ketszim97/TO_220_Buck/Renders/Photos/149419925_792506014680006_8886446949957860765_n.jpg

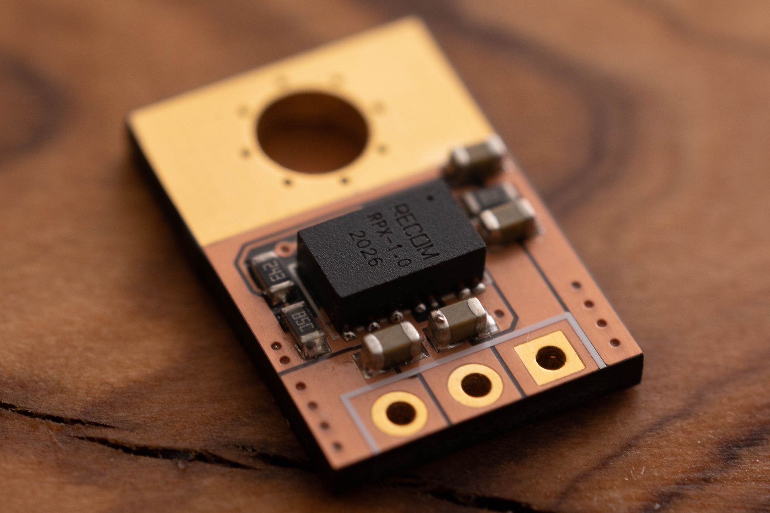
Renders/Photos/149419925_792506014680006_8886446949957860765_n.jpg
