ketszim97/TO_220_Buck/Renders/Photos/149459865_3474213502690533_5137175268388201964_n.jpg

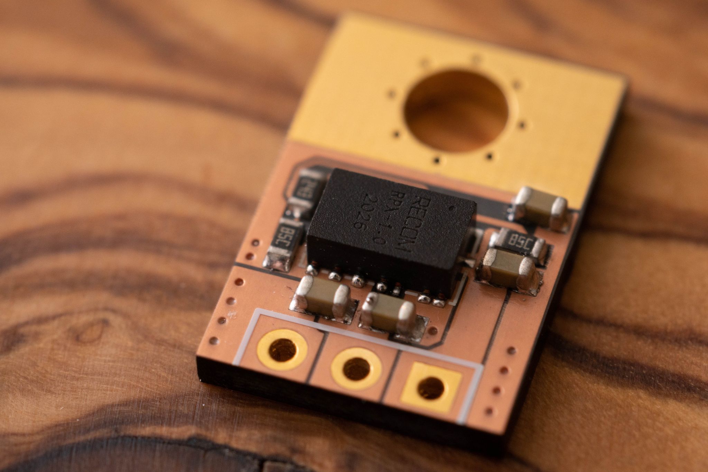
Renders/Photos/149459865_3474213502690533_5137175268388201964_n.jpg
