ketszim97/TO_220_Buck/Renders/Photos/149528836_711852932822343_8148399697909948898_n.jpg

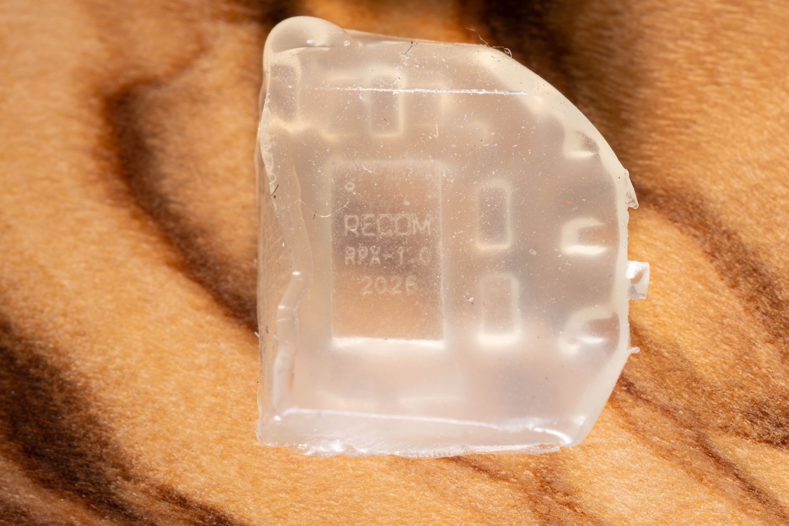
Renders/Photos/149528836_711852932822343_8148399697909948898_n.jpg
