ketszim97/TO_220_Buck/Renders/Photos/149537447_1244964915901211_925511400282466722_n.jpg

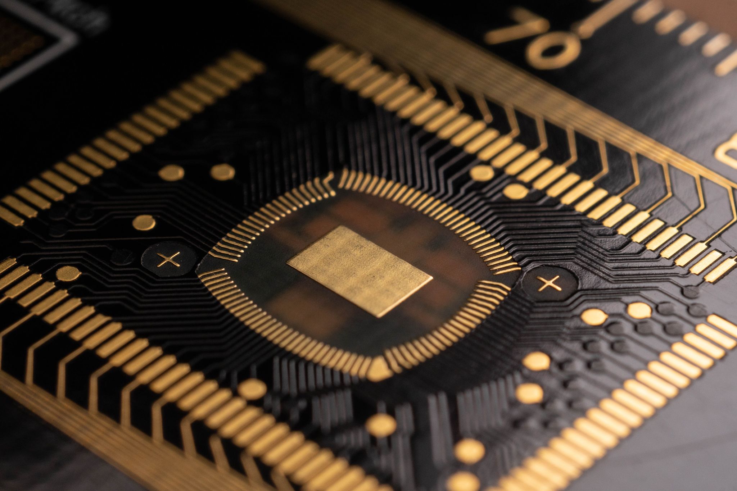
Renders/Photos/149537447_1244964915901211_925511400282466722_n.jpg
