ketszim97/TO_220_Buck/Renders/Photos/149566812_3517663008360148_2053222494374139507_n.jpg

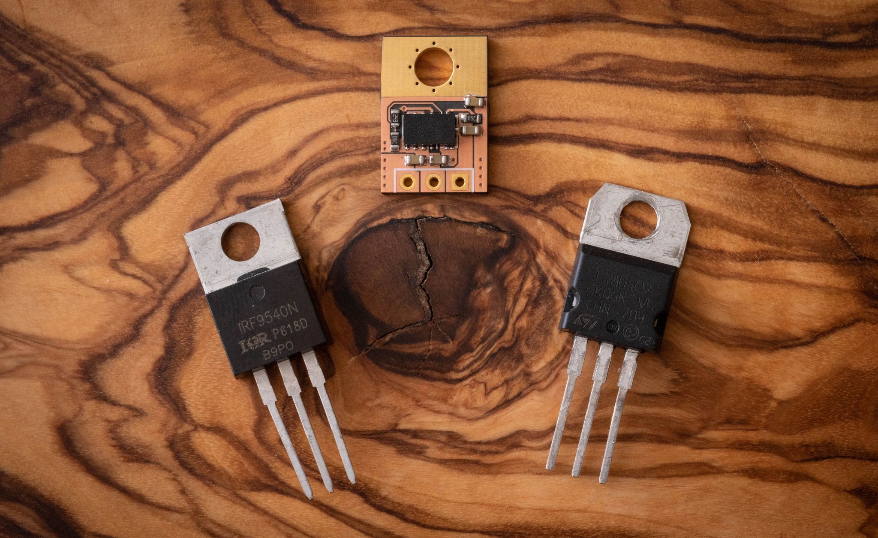
Renders/Photos/149566812_3517663008360148_2053222494374139507_n.jpg
