ketszim97/TO_220_Buck/Renders/Photos/149648833_326271058803372_157924160653448781_n.jpg

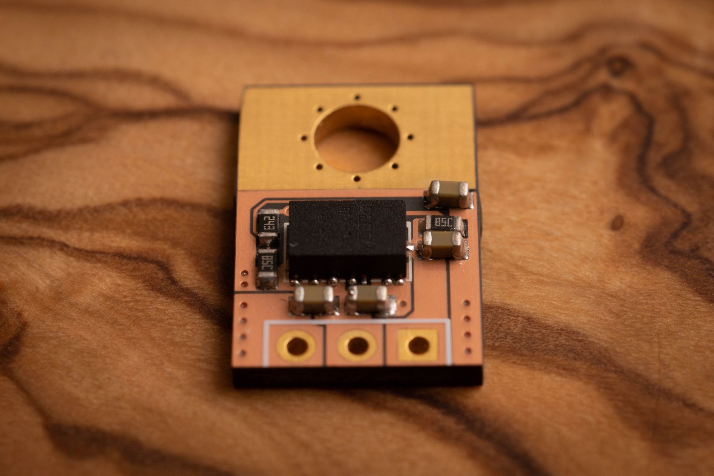
Renders/Photos/149648833_326271058803372_157924160653448781_n.jpg
