ketszim97/TO_220_Buck/Renders/Photos/149690482_248480446752142_3542841920429757807_n.jpg

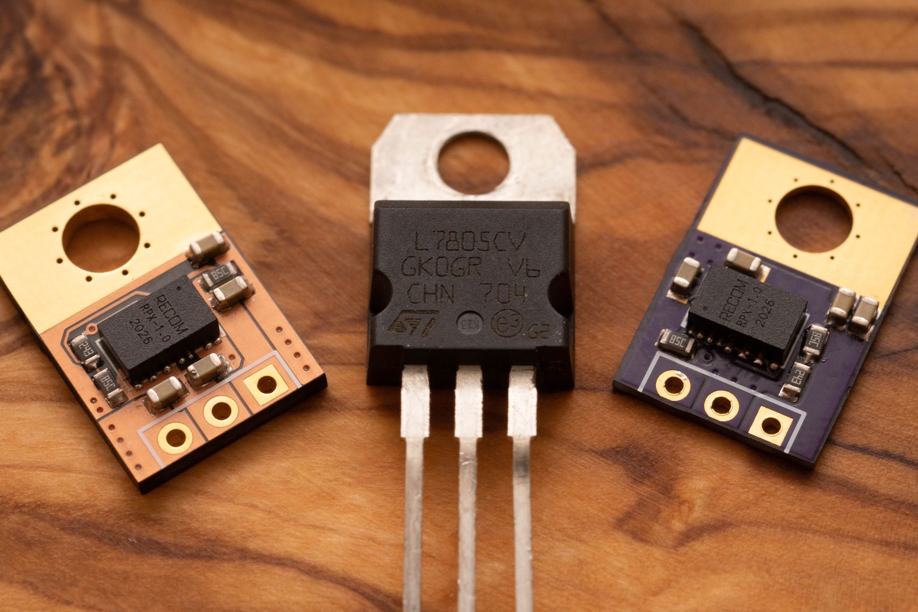
Renders/Photos/149690482_248480446752142_3542841920429757807_n.jpg
