ketszim97/TO_220_Buck/Renders/Photos/149705849_492895295441886_4602141825027261925_n.jpg

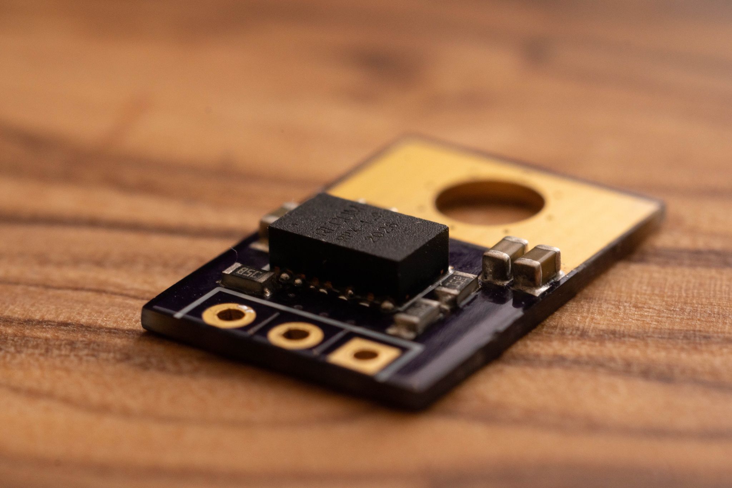
Renders/Photos/149705849_492895295441886_4602141825027261925_n.jpg
