ketszim97/TO_220_Buck/Renders/Photos/149872428_330163285035907_6420087823227812447_n.jpg

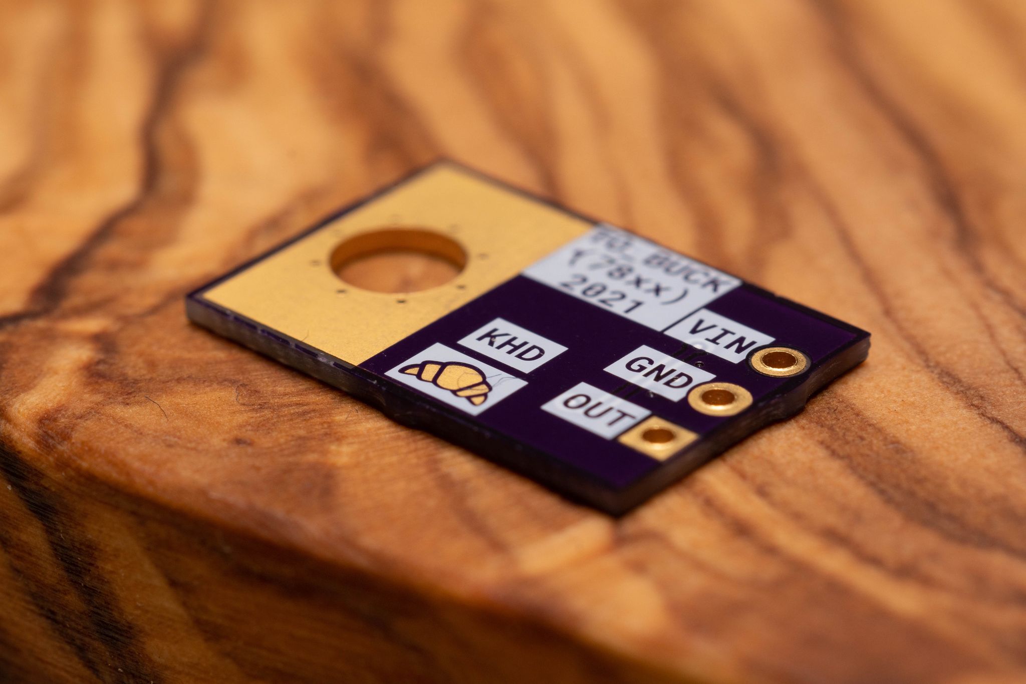
Renders/Photos/149872428_330163285035907_6420087823227812447_n.jpg
