ketszim97/TO_220_Buck/Renders/Photos/149902373_492424528822275_8873897516138256639_n.jpg

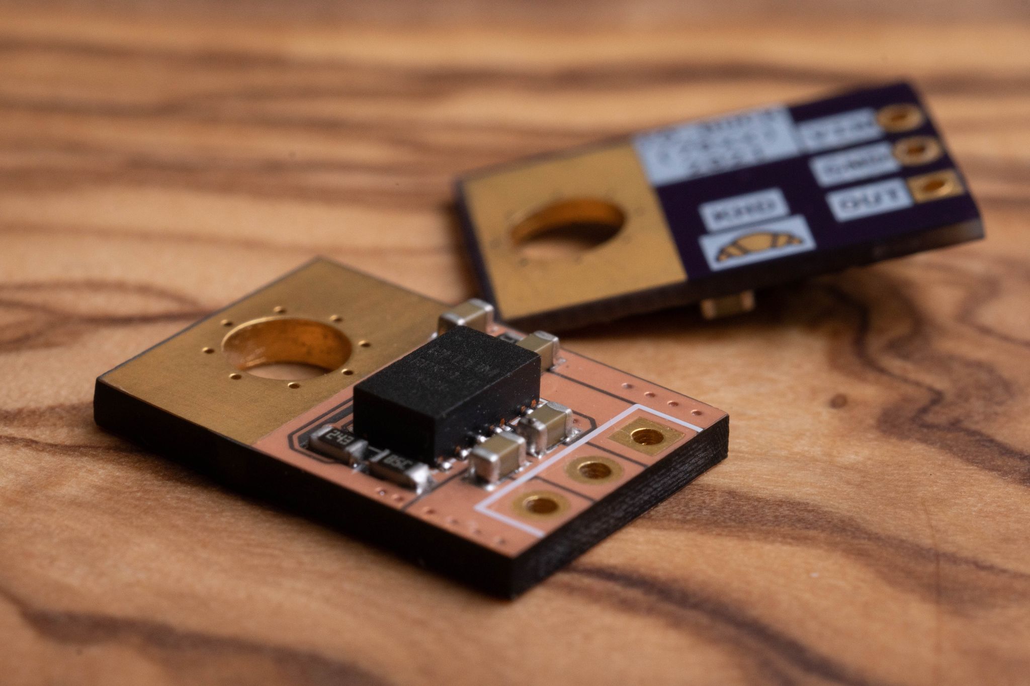
Renders/Photos/149902373_492424528822275_8873897516138256639_n.jpg
