ketszim97/TO_220_Buck/Renders/Photos/149912720_1985792348225276_4884634092275549586_n.jpg

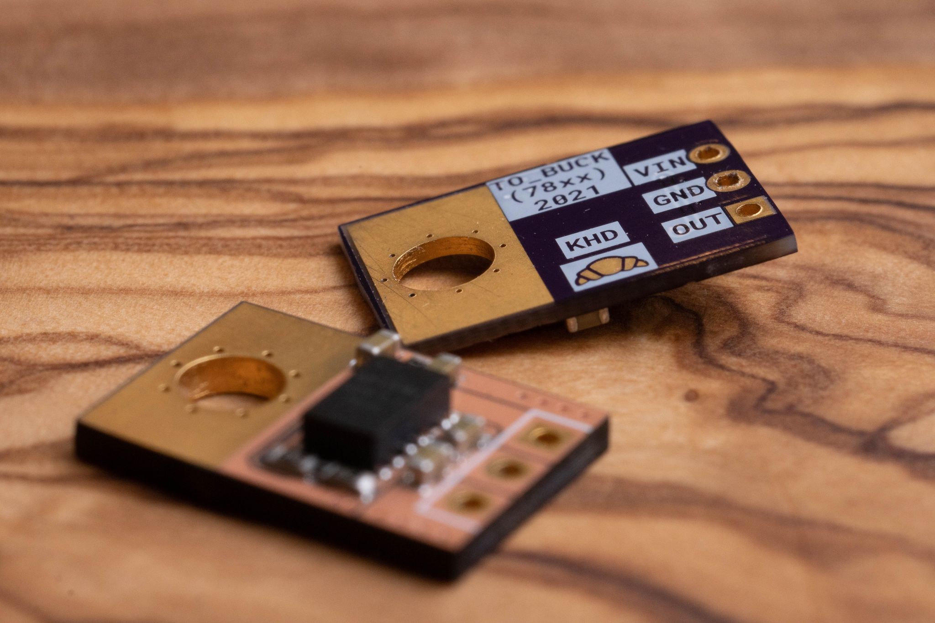
Renders/Photos/149912720_1985792348225276_4884634092275549586_n.jpg
