ketszim97/TO_220_Buck/Renders/Photos/149937713_420765092525831_9167104044929866773_n.jpg

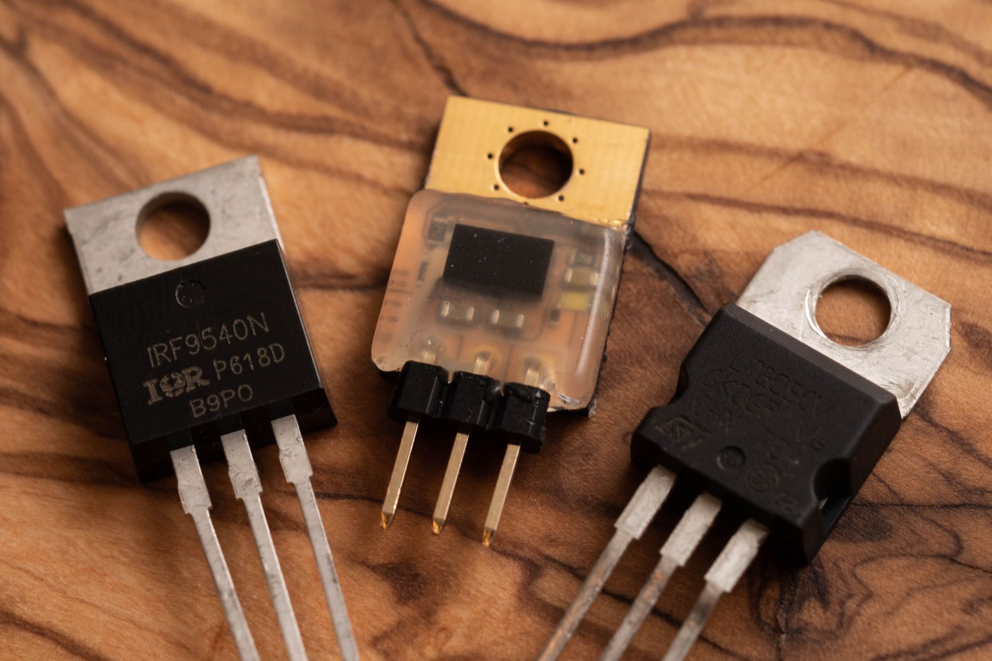
Renders/Photos/149937713_420765092525831_9167104044929866773_n.jpg
