ketszim97/TO_220_Buck/Renders/Photos/149948058_841184139772258_1999186233133940931_n.jpg

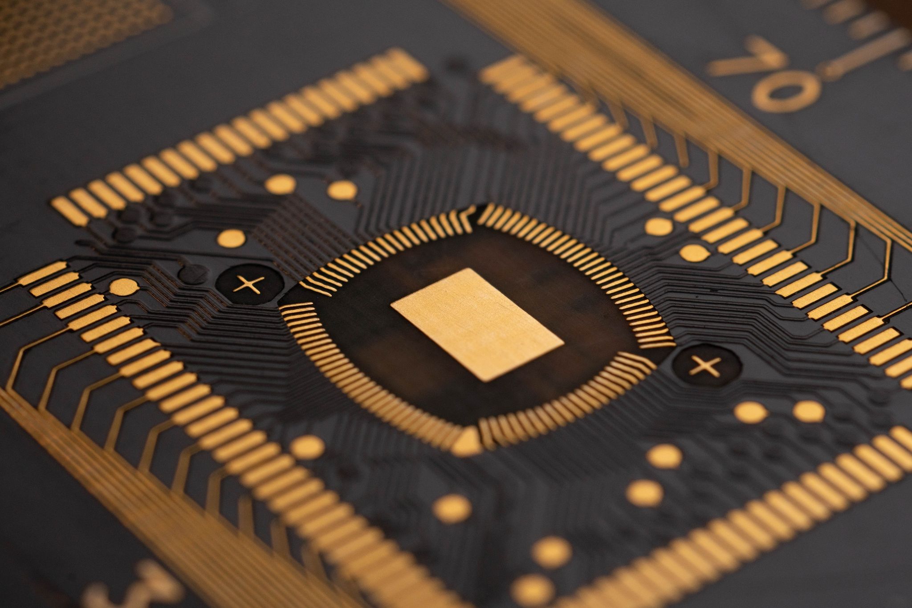
Renders/Photos/149948058_841184139772258_1999186233133940931_n.jpg
