ketszim97/TO_220_Buck/Renders/Photos/150226257_426522105130324_2970456600032907826_n.jpg

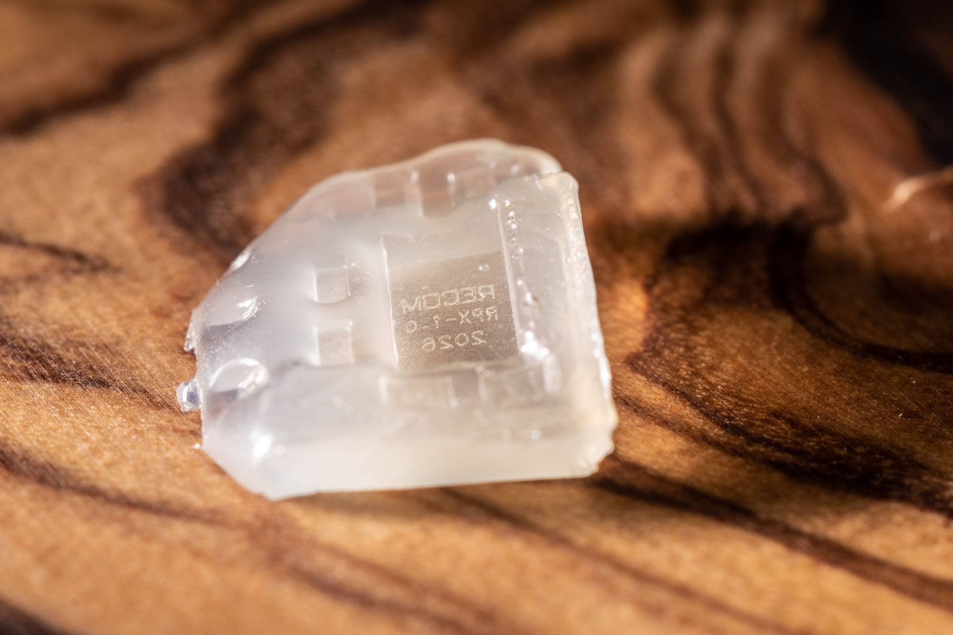
Renders/Photos/150226257_426522105130324_2970456600032907826_n.jpg
