ketszim97/TO_220_Buck/Renders/Photos/150301503_871936146932854_7972251521524092523_n.jpg

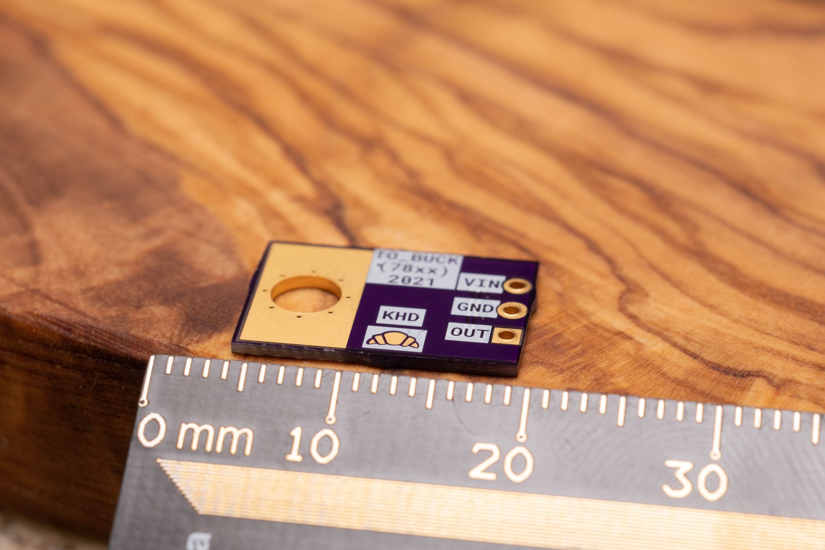
Renders/Photos/150301503_871936146932854_7972251521524092523_n.jpg
